cepetr/blue2joy/firmware/src/btjp/btjp_commands.c

/*
 * This file is part of the Blue2Joy project
 * (https://github.com/cepetr/blue2joy).
 * Copyright (c) 2025
 *
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
 * You should have received a copy of the GNU General Public License
 * along with this program. If not, see <http://www.gnu.org/licenses/>.
 */

#include <assert.h>
#include <stddef.h>
#include <string.h>
#include <stdlib.h>

#include <zephyr/logging/log.h>
#include <hw_id.h>
#include <app_version.h>

#include <devmgr/devmgr.h>
#include <mapper/mapper.h>
#include <mapper/joy_port.h>

#include "btjp.h"
#include "btjp_utils.h"
#include "btjp_msg.h"

LOG_MODULE_REGISTER(btj_cmd, LOG_LEVEL_DBG);

#define CHECK_REQ_SIZE(req, expected_size)                                                         \
    do {                                                                                           \
        if ((req)->hdr.size != (expected_size)) {                                                  \
            return BTJP_ERR_INVALID_REQ;                                                           \
        }                                                                                          \
    } while (0)

#define CHECK_REQ_ARG(condition)                                                                   \
    do {                                                                                           \
        if (!(condition)) {                                                                        \
            return BTJP_ERR_INVALID_ARG;                                                           \
        }                                                                                          \
    } while (0)

static void hw_id_get_bytes(uint8_t *buff, size_t buff_size)
{
    assert(buff_size == 8);

    memset(buff, 0, buff_size);

    // Get hexadecimal representation of HW ID
    char str[HW_ID_LEN];
    if (hw_id_get(str, sizeof(str)) != 0) {
        return;
    }

    // Parse hex string into bytes
    // (assumes valid hex string)
    for (size_t i = 0; i < buff_size; i++) {
        char byte_str[3] = {str[i * 2], str[i * 2 + 1], 0};
        buff[i] = (uint8_t)strtol(byte_str, NULL, 16);
    }
}

static btjp_status_t btjp_handle_request(const btjp_req_t *req, btjp_rsp_t *rsp)
{
    switch (req->hdr.msg_id) {
    case BTJP_MSG_GET_API_VERSION: {
        CHECK_REQ_SIZE(req, 0);
        rsp->hdr.size = sizeof(rsp->get_api_version);
        rsp->get_api_version.major = 1;
        rsp->get_api_version.minor = 0;
    } break;

    case BTJP_MSG_GET_SYS_INFO: {
        CHECK_REQ_SIZE(req, 0);
        rsp->hdr.size = sizeof(rsp->get_sys_info);
        hw_id_get_bytes(rsp->get_sys_info.hw_id, sizeof(rsp->get_sys_info.hw_id));
        rsp->get_sys_info.sw_version = APPVERSION;
        rsp->get_sys_info.hw_version = 0;
    } break;

    case BTJP_MSG_SET_DEV_CONFIG: {
        CHECK_REQ_SIZE(req, sizeof(req->set_dev_config));

        bt_addr_le_t addr;
        dev_addr_to_bt_addr_le(&req->set_dev_config.addr, &addr);

        devmgr_device_config_t config = {0};
        config.profile = req->set_dev_config.profile;

        int err = devmgr_set_device_config(&addr, &config, true);
        if (err != 0) {
            return BTJP_ERR_INVALID_ARG;
        }
    } break;

    case BTJP_MSG_SET_PIN_CONFIG: {
        CHECK_REQ_SIZE(req, sizeof(req->set_pin_config));

        mapper_profile_t profile;
        int err = mapper_get_profile(req->set_pin_config.profile, &profile);
        if (err != 0) {
            LOG_ERR("Invalid profile #%d", req->set_pin_config.profile);
            return BTJP_ERR_INVALID_ARG;
        }

        mapper_pin_config_t *config = profile_pin(&profile, req->set_pin_config.pin_id);
        if (config == NULL) {
            LOG_ERR("Invalid pin ID %d", req->set_pin_config.pin_id);
            return BTJP_ERR_INVALID_ARG;
        }

        config->source = req->set_pin_config.source;
        config->invert = req->set_pin_config.invert ? true : false;
        config->hat_switch = req->set_pin_config.hat_switch;
        config->threshold = req->set_pin_config.threshold;
        config->hysteresis = req->set_pin_config.hysteresis;

        err = mapper_set_profile(req->set_pin_config.profile, &profile, true);
        if (err != 0) {
            return BTJP_ERR_INVALID_ARG;
        }
    } break;

    case BTJP_MSG_SET_POT_CONFIG: {
        CHECK_REQ_SIZE(req, sizeof(req->set_pot_config));

        mapper_profile_t profile;
        int err = mapper_get_profile(req->set_pot_config.profile, &profile);
        if (err != 0) {
            LOG_ERR("Invalid profile #%d", req->set_pot_config.profile);
            return BTJP_ERR_INVALID_ARG;
        }

        mapper_pot_config_t *config = profile_pot(&profile, req->set_pot_config.pin_id);
        if (config == NULL) {
            LOG_ERR("Invalid pin ID %d", req->set_pot_config.pin_id);
            return BTJP_ERR_INVALID_ARG;
        }

        config->source = req->set_pot_config.source;
        config->low = req->set_pot_config.low;
        config->high = req->set_pot_config.high;

        err = mapper_set_profile(req->set_pot_config.profile, &profile, true);
        if (err != 0) {
            return BTJP_ERR_INVALID_ARG;
        }
    } break;

    case BTJP_MSG_SET_INTG_CONFIG: {
        CHECK_REQ_SIZE(req, sizeof(req->set_intg_config));

        mapper_profile_t profile;
        int err = mapper_get_profile(req->set_intg_config.profile, &profile);
        if (err != 0) {
            LOG_ERR("Invalid profile #%d", req->set_intg_config.profile);
            return BTJP_ERR_INVALID_ARG;
        }

        mapper_intg_config_t *config = profile_intg(&profile, req->set_intg_config.intg_id);
        if (config == NULL) {
            LOG_ERR("Invalid integrator ID %d", req->set_intg_config.intg_id);
            return BTJP_ERR_INVALID_ARG;
        }

        config->source = req->set_intg_config.source;
        config->mode = (mapper_intr_mode_t)req->set_intg_config.mode;
        config->dead_zone = req->set_intg_config.dead_zone;
        config->gain = req->set_intg_config.gain;
        config->max = req->set_intg_config.max;

        err = mapper_set_profile(req->set_intg_config.profile, &profile, true);
        if (err != 0) {
            return BTJP_ERR_INVALID_ARG;
        }
    } break;

    case BTJP_MSG_SET_MODE: {
        CHECK_REQ_SIZE(req, sizeof(req->set_mode));
        CHECK_REQ_ARG(req->set_mode.mode <= DEVMGR_MODE_MANUAL);

        devmgr_mode_t mode = (devmgr_mode_t)req->set_mode.mode;
        bool restart = req->set_mode.restart ? true : false;

        devmgr_set_mode(mode, restart);
    } break;

    case BTJP_MSG_SET_PROFILE: {
        CHECK_REQ_SIZE(req, sizeof(req->set_profile));

        mapper_profile_t profile = {0};

        for (int i = 0; i < ARRAY_SIZE(req->set_profile.pins); i++) {
            mapper_pin_config_t *pin = profile_pin(&profile, i);
            pin->source = req->set_profile.pins[i].source;
            pin->invert = req->set_profile.pins[i].invert ? true : false;
            pin->hat_switch = req->set_profile.pins[i].hat_switch;
            pin->threshold = req->set_profile.pins[i].threshold;
            pin->hysteresis = req->set_profile.pins[i].hysteresis;
        }

        for (int i = 0; i < ARRAY_SIZE(req->set_profile.pots); i++) {
            mapper_pot_config_t *pot = profile_pot(&profile, i);
            pot->source = req->set_profile.pots[i].source;
            pot->low = req->set_profile.pots[i].low;
            pot->high = req->set_profile.pots[i].high;
        }

        for (int i = 0; i < ARRAY_SIZE(req->set_profile.intgs); i++) {
            mapper_intg_config_t *intg = profile_intg(&profile, i);
            intg->source = req->set_profile.intgs[i].source;
            intg->mode = (mapper_intr_mode_t)req->set_profile.intgs[i].mode;
            intg->dead_zone = req->set_profile.intgs[i].dead_zone;
            intg->gain = req->set_profile.intgs[i].gain;
            intg->max = req->set_profile.intgs[i].max;
        }

        // Save updated profile
        int err = mapper_set_profile(req->set_profile.profile, &profile, true);
        if (err) {
            return BTJP_ERR_INVALID_ARG;
        }
    } break;

    case BTJP_MSG_FACTORY_RESET: {
        CHECK_REQ_SIZE(req, 0);
        LOG_ERR("Factory reset over BTJP is not implemented");
        return BTJP_ERR_UNKNOWN_MSG;
    } break;

    case BTJP_MSG_SET_JOY_PORT_MODE: {
        CHECK_REQ_SIZE(req, sizeof(req->set_joy_port_mode));

        joy_port_mode_t mode = JOY_PORT_MODE_NORMAL;

        switch (req->set_joy_port_mode.mode) {
        case BTJP_JOY_PORT_MODE_NORMAL:
            mode = JOY_PORT_MODE_NORMAL;
            break;
        case BTJP_JOY_PORT_MODE_SPI:
            mode = JOY_PORT_MODE_SPI;
            break;
        case BTJP_JOY_PORT_MODE_UART:
            mode = JOY_PORT_MODE_UART;
            break;
        default:
            return BTJP_ERR_INVALID_ARG;
        }

        int err = joy_port_set_mode(mode);
        if (err != 0) {
            return BTJP_ERR_INVALID_ARG;
        }
    } break;

    case BTJP_MSG_START_SCANNING: {
        CHECK_REQ_SIZE(req, 0);

        int err = devmgr_start_scanning();
        if (err != 0) {
            return BTJP_ERR_INVALID_ARG;
        }
    } break;

    case BTJP_MSG_STOP_SCANNING: {
        CHECK_REQ_SIZE(req, 0);

        devmgr_stop_scanning();
    } break;

    case BTJP_MSG_CONNECT_DEVICE: {
        CHECK_REQ_SIZE(req, sizeof(req->connect_device));

        bt_addr_le_t addr;
        dev_addr_to_bt_addr_le(&req->connect_device.addr, &addr);

        int err = devmgr_connect(&addr);
        if (err != 0) {
            return BTJP_ERR_INVALID_ARG;
        }
    } break;

    case BTJP_MSG_DELETE_DEVICE: {
        CHECK_REQ_SIZE(req, sizeof(req->delete_device));

        bt_addr_le_t addr;
        dev_addr_to_bt_addr_le(&req->delete_device.addr, &addr);

        int err = devmgr_delete_device(&addr);
        if (err != 0) {
            return BTJP_ERR_INVALID_ARG;
        }
    } break;

    case BTJP_MSG_PRESS_KEY: {
        CHECK_REQ_SIZE(req, sizeof(req->press_key));

        uint8_t keycode = req->press_key.keycode;

        mapper_press_key(keycode);
    } break;

    default:
        return BTJP_ERR_UNKNOWN_MSG;
    }

    return BTJP_ERR_NONE;
}

size_t btjp_handle_message(const void *inbuff, size_t insize, void *outbuff, size_t outsize)
{
    if (insize < sizeof(btjp_msg_header_t) || outsize < sizeof(btjp_rsp_t)) {
        LOG_ERR("Invalid buffer size");
        return 0;
    }

    const btjp_req_t *req = (const btjp_req_t *)inbuff;
    btjp_rsp_t *rsp = (btjp_rsp_t *)outbuff;

    if ((req->hdr.flags & BTJP_MSG_TYPE_MASK) != BTJP_MSG_TYPE_REQUEST) {
        // Not a request message
        LOG_ERR("Not a request message");
        return 0;
    }

    LOG_HEXDUMP_INF(inbuff, insize, "Received message");

    memset(rsp, 0, outsize);
    rsp->hdr.seq = req->hdr.seq;
    rsp->hdr.msg_id = req->hdr.msg_id;
    rsp->hdr.flags = BTJP_MSG_TYPE_RESPONSE;

    btjp_status_t status = btjp_handle_request(req, rsp);

    if (status != BTJP_ERR_NONE) {
        LOG_ERR("Request handling error {status: %d}", status);
        rsp->hdr.flags = BTJP_MSG_TYPE_ERROR;
        rsp->error.code = status;
        rsp->hdr.size = sizeof(rsp->error);
    }

    LOG_HEXDUMP_INF(outbuff, sizeof(btjp_msg_header_t) + rsp->hdr.size, "Sending response");

    return sizeof(btjp_msg_header_t) + rsp->hdr.size;
}

// Checks whether the buffer contains a BTJP_MSG_GET_API_VERSION request.
bool btjp_is_sync_request(const uint8_t *inbuff, size_t insize)
{
    if (insize < sizeof(btjp_msg_header_t)) {
        return false;
    }

    const btjp_msg_header_t *hdr = (const btjp_msg_header_t *)inbuff;

    return (hdr->flags & BTJP_MSG_TYPE_MASK) == BTJP_MSG_TYPE_REQUEST &&
           hdr->msg_id == BTJP_MSG_GET_API_VERSION;
}
