cepetr/blue2joy/firmware/src/io/io_pot.c

/*
 * This file is part of the Blue2Joy project
 * (https://github.com/cepetr/blue2joy).
 * Copyright (c) 2025
 *
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
 * You should have received a copy of the GNU General Public License
 * along with this program. If not, see <http://www.gnu.org/licenses/>.
 */

#include <zephyr/kernel.h>
#include <zephyr/logging/log.h>
#include <zephyr/drivers/gpio.h>
#include <zephyr/irq.h>

#include <nrfx_comp.h>
#include <nrfx_timer.h>
#include <nrfx_ppi.h>
#include <nrfx_gpiote.h>

#include "io_pot.h"

LOG_MODULE_REGISTER(btj_io_pot, LOG_LEVEL_DBG);

static const nrfx_timer_t timer = NRFX_TIMER_INSTANCE(2);
static const nrfx_gpiote_t gpiote = NRFX_GPIOTE_INSTANCE(0);

static const struct gpio_dt_spec joy_p0_chg = GPIO_DT_SPEC_GET(DT_ALIAS(joy_p0_chg), gpios);

typedef struct {
    uint8_t keycodes[8];
    uint8_t count;
    bool pressed;
} io_pot_kbd_t;

typedef struct {
    uint8_t gpiote_p0_chg; // GPIOTE channel for POT0 charging
    uint8_t gpiote_p1_chg; // GPIOTE channel for POT1 charging

    nrf_ppi_channel_t ppi_start_cycle; // PPI channel to start the timer cycle
    nrf_ppi_channel_t ppi_p0_charge;   // PPI channel for POT0 charging
    nrf_ppi_channel_t ppi_p1_charge;   // PPI channel for POT1 charging
    nrf_ppi_channel_t ppi_end_cycle;   // PPI channel to end the timer cycle

    // Simple averaging filter state
    struct {
        uint8_t buf[10];
        uint8_t pos;
        uint16_t sum;
        uint32_t time;
    } filter;

    // Measured period in milliseconds
    atomic_t period;

    atomic_t cc_value[IO_POT_COUNT];

    // Encoder simulator position
    int32_t enc_pos[IO_POT_COUNT];

    // Keyboard simulation
    io_pot_kbd_t kbd;

} io_pot_drv_t;

io_pot_drv_t g_io_pot_drv;

// Forward declarations
static void io_pot_process_keypresses(void);

static void comparator_handler(nrf_comp_event_t event)
{
    io_pot_drv_t *drv = &g_io_pot_drv;

    uint32_t now = k_uptime_get_32();

    if (drv->filter.time > 0) {
        uint32_t diff = now - drv->filter.time;

        // Calculate moving average
        drv->filter.sum -= drv->filter.buf[drv->filter.pos];
        drv->filter.buf[drv->filter.pos] = diff;
        drv->filter.sum += drv->filter.buf[drv->filter.pos];
        drv->filter.pos = (drv->filter.pos + 1) % ARRAY_SIZE(drv->filter.buf);
    }

    atomic_set(&drv->period, (drv->filter.sum / ARRAY_SIZE(drv->filter.buf)));

    drv->filter.time = now;

    // Process pending key presses for keyboard emulation
    io_pot_process_keypresses();
}

static void timer_handler(nrf_timer_event_t event_type, void *p_context)
{
    io_pot_drv_t *drv = &g_io_pot_drv;

    // Since TIMER CC registers are not double buffered, we need to
    // update them in the timer interrupt handler - just after the
    // compare event has occurred.

    if (event_type == NRF_TIMER_EVENT_COMPARE0) {
        uint32_t cc_value = atomic_get(&drv->cc_value[0]);
        nrfx_timer_compare(&timer, NRF_TIMER_CC_CHANNEL0, cc_value, true);
    } else if (event_type == NRF_TIMER_EVENT_COMPARE1) {
        uint32_t cc_value = atomic_get(&drv->cc_value[1]);
        nrfx_timer_compare(&timer, NRF_TIMER_CC_CHANNEL1, cc_value, true);
    }
}

int io_pot_init(void)
{
    io_pot_drv_t *drv = &g_io_pot_drv;

    nrfx_gpiote_pin_t pin_p0_chg = NRF_GPIO_PIN_MAP(0, 15); // Pin for POT0 charging
    nrfx_gpiote_pin_t pin_p1_chg = NRF_GPIO_PIN_MAP(0, 19); // Pin for POT1 charging

    // Get pin/port from joy_p0_chg
    gpio_pin_configure_dt(&joy_p0_chg, GPIO_OUTPUT_LOW);

    // -------------------------------------------------------------------------------
    // Initialize the analog comparator
    //
    // V+ = (Vcap + 5V) / 4 - when POT0 charging is active
    // V+ = Vcap / 2 - when POT0 charging is inactive
    // V- = 1.4V (Upper threshold) or 1.3V (Lower threshold)
    //
    // The comparator is used to monitor the POT0 voltage in order to detect
    // when the POKEY chip releases its discharge transistors,
    // indicating that the POKEY counter has been reset and starts counting.
    //
    // The comparator is automatically stopped after the UP event
    // and is started again at the end of the cycle (which is set to 17 ms).
    // -------------------------------------------------------------------------------

    nrfx_comp_config_t comp_config = NRFX_COMP_DEFAULT_CONFIG(NRF_COMP_INPUT_4);

    comp_config.reference = NRF_COMP_REF_INT_2V4;
    comp_config.main_mode = NRF_COMP_MAIN_MODE_SE;
    comp_config.threshold.th_down = NRFX_COMP_VOLTAGE_THRESHOLD_TO_INT(1.3, 2.4);
    comp_config.threshold.th_up = NRFX_COMP_VOLTAGE_THRESHOLD_TO_INT(1.4, 2.4);
    comp_config.speed_mode = NRF_COMP_SP_MODE_HIGH;
    comp_config.hyst = NRF_COMP_HYST_NO_HYST;

    nrfx_err_t err;

    err = nrfx_comp_init(&comp_config, comparator_handler);
    if (err != NRFX_SUCCESS) {
        LOG_ERR("nrfx_comp_init error: %08x", err);
        return -EIO;
    }

    // Connect COMP_IRQ to nrfx_comp_irq_handler - TODO: do we need this??
    IRQ_CONNECT(COMP_LPCOMP_IRQn, IRQ_PRIO_LOWEST, nrfx_isr, nrfx_comp_irq_handler, 0);

    nrfx_comp_start(NRF_COMP_INT_UP_MASK, NRFX_COMP_SHORT_STOP_AFTER_UP_EVT);

    // -------------------------------------------------------------------------------
    // Initialize the timer
    //
    // The timer is used to precisely control the charging outputs
    // of the POT0 and POT1 capacitors. It is started a few microseconds after
    // we detect that the POKEY chip has released its discharge transistors.
    //
    // Two compare channels are used to control the time when we
    // activate the MOSFETs that rapidly charge the POT0 and POT1 capacitors.
    //
    // Channel 0 - triggers POT0 charging
    // Channel 1 - triggers POT1 charging
    // Channel 2 - starts comparator
    // Channel 3 - resets the timer
    // -------------------------------------------------------------------------------

    nrfx_timer_config_t timer_config = NRFX_TIMER_DEFAULT_CONFIG(NRFX_MHZ_TO_HZ(1));
    timer_config.mode = NRF_TIMER_MODE_TIMER;
    timer_config.bit_width = NRF_TIMER_BIT_WIDTH_16;

    err = nrfx_timer_init(&timer, &timer_config, timer_handler);
    if (err != NRFX_SUCCESS) {
        LOG_ERR("nrfx_timer_init error: %08x", err);
        return -EIO;
    }

    IRQ_CONNECT(TIMER2_IRQn, IRQ_PRIO_LOWEST, nrfx_isr, nrfx_timer_2_irq_handler, 0)

    uint32_t initial_cc_value = 16000; // => IO_POT_MAX_VAL

    atomic_set(&drv->cc_value[0], initial_cc_value);
    atomic_set(&drv->cc_value[1], initial_cc_value);

    nrfx_timer_compare(&timer, NRF_TIMER_CC_CHANNEL0, initial_cc_value, true);
    nrfx_timer_compare(&timer, NRF_TIMER_CC_CHANNEL1, initial_cc_value, true);

    nrfx_timer_compare(&timer, NRF_TIMER_CC_CHANNEL2, 17000, false); // 17ms

    nrfx_timer_extended_compare(&timer, NRF_TIMER_CC_CHANNEL3, 25000,
                                NRF_TIMER_SHORT_COMPARE3_CLEAR_MASK, false);

    nrfx_timer_enable(&timer);

    // -------------------------------------------------------------------------------
    // Outputs for capacitor charging
    //
    // The POT0 and POT1 charging outputs are controlled by GPIOTE,
    // allowing us to activate them via PPI channels.
    // -------------------------------------------------------------------------------

    // POT0 charging

    err = nrfx_gpiote_channel_alloc(&gpiote, &drv->gpiote_p0_chg);
    if (err != NRFX_SUCCESS) {
        LOG_ERR("nrfx_gpiote_channel_alloc error: %08x", err);
        return -EIO;
    }

    nrfx_gpiote_output_config_t out_config = NRFX_GPIOTE_DEFAULT_OUTPUT_CONFIG;

    nrfx_gpiote_task_config_t task_config = {
        .task_ch = drv->gpiote_p0_chg,
        .polarity = GPIOTE_CONFIG_POLARITY_LoToHi,
        .init_val = NRF_GPIOTE_INITIAL_VALUE_LOW,
    };

    err = nrfx_gpiote_output_configure(&gpiote, pin_p0_chg, &out_config, &task_config);
    if (err != NRFX_SUCCESS) {
        LOG_ERR("nrfx_gpiote_out_init error: %08x", err);
        return -EIO;
    }

    nrfx_gpiote_out_task_enable(&gpiote, pin_p0_chg);

    // POT1 charging

    err = nrfx_gpiote_channel_alloc(&gpiote, &drv->gpiote_p1_chg);
    if (err != NRFX_SUCCESS) {
        LOG_ERR("nrfx_gpiote_channel_alloc error: %08x", err);
        return -EIO;
    }

    nrfx_gpiote_output_config_t out_config2 = NRFX_GPIOTE_DEFAULT_OUTPUT_CONFIG;

    nrfx_gpiote_task_config_t task_config2 = {
        .task_ch = drv->gpiote_p1_chg,
        .polarity = GPIOTE_CONFIG_POLARITY_LoToHi,
        .init_val = NRF_GPIOTE_INITIAL_VALUE_LOW,
    };

    err = nrfx_gpiote_output_configure(&gpiote, pin_p1_chg, &out_config2, &task_config2);
    if (err != NRFX_SUCCESS) {
        LOG_ERR("nrfx_gpiote_out_init error: %08x", err);
        return -EIO;
    }

    nrfx_gpiote_out_task_enable(&gpiote, pin_p1_chg);

    // -------------------------------------------------------------------------------
    // PPI channels
    //
    // PPI channels connect the analog comparator, timer, and GPIOTE peripherals.
    //
    // PPI usage:
    // 1. COMP_UP event -> TIMER_CLEAR task & GPIOTE_CLR task (disable POT0 charging)
    // 2. TIMER_COMPARE0 event -> GPIOTE_SET task (enable POT0 charging)
    // 3. TIMER_COMPARE1 event -> GPIOTE_SET task (enable POT1 charging)
    // 4. TIMER_COMPARE3 event -> COMP_START task (restart comparator)
    // -------------------------------------------------------------------------------

    uint32_t eep;
    uint32_t tep;

    // --------------------------------------------------------------------
    // ppi_start_cycle
    //
    // Comparator UP event:
    //   -> clears the timer
    //   -> disables the POT0 charging output

    err = nrfx_ppi_channel_alloc(&drv->ppi_start_cycle);
    if (err != NRFX_SUCCESS) {
        LOG_ERR("nrfx_ppi_channel_alloc error: %08x", err);
        return -EIO;
    }

    eep = nrfx_comp_event_address_get(NRF_COMP_EVENT_UP);
    tep = nrfx_timer_task_address_get(&timer, NRF_TIMER_TASK_CLEAR);

    err = nrfx_ppi_channel_assign(drv->ppi_start_cycle, eep, tep);
    if (err != NRFX_SUCCESS) {
        LOG_ERR("nrfx_ppi_channel_assign error: %08x", err);
        return -EIO;
    }

    tep = nrfx_gpiote_clr_task_address_get(&gpiote, pin_p0_chg);
    err = nrfx_ppi_channel_fork_assign(drv->ppi_start_cycle, tep);
    if (err != NRFX_SUCCESS) {
        LOG_ERR("nrfx_ppi_channel_fork_assign error: %08x", err);
        return -EIO;
    }

    err = nrfx_ppi_channel_enable(drv->ppi_start_cycle);
    if (err != NRFX_SUCCESS) {
        LOG_ERR("Failed enabling ppi channel: %08x", err);
        return -EIO;
    }

    // --------------------------------------------------------------------
    // ppi_p0_charge
    //
    // Timer COMPARE0 event:
    //   -> enables the POT0 charging output

    err = nrfx_ppi_channel_alloc(&drv->ppi_p0_charge);
    if (err != NRFX_SUCCESS) {
        LOG_ERR("nrfx_ppi_channel_alloc error: %08x", err);
        return -EIO;
    }

    eep = nrfx_timer_event_address_get(&timer, NRF_TIMER_EVENT_COMPARE0);
    tep = nrfx_gpiote_set_task_address_get(&gpiote, pin_p0_chg);

    err = nrfx_ppi_channel_assign(drv->ppi_p0_charge, eep, tep);
    if (err != NRFX_SUCCESS) {
        LOG_ERR("nrfx_ppi_channel_assign error: %08x", err);
        return -EIO;
    }

    err = nrfx_ppi_channel_enable(drv->ppi_p0_charge);
    if (err != NRFX_SUCCESS) {
        LOG_ERR("Failed enabling ppi channel: %08x", err);
        return -EIO;
    }

    // --------------------------------------------------------------------
    // ppi_p1_charge
    //
    // Timer COMPARE1 event:
    //   -> enables the POT1 charging output

    err = nrfx_ppi_channel_alloc(&drv->ppi_p1_charge);
    if (err != NRFX_SUCCESS) {
        LOG_ERR("nrfx_ppi_channel_alloc error: %08x", err);
        return -EIO;
    }

    eep = nrfx_timer_event_address_get(&timer, NRF_TIMER_EVENT_COMPARE1);
    tep = nrfx_gpiote_set_task_address_get(&gpiote, pin_p1_chg);

    err = nrfx_ppi_channel_assign(drv->ppi_p1_charge, eep, tep);
    if (err != NRFX_SUCCESS) {
        LOG_ERR("nrfx_ppi_channel_assign error: %08x", err);
        return -EIO;
    }

    err = nrfx_ppi_channel_enable(drv->ppi_p1_charge);
    if (err != NRFX_SUCCESS) {
        LOG_ERR("Failed enabling ppi channel: %08x", err);
        return -EIO;
    }

    // --------------------------------------------------------------------
    // ppi_end_cycle
    //
    // Timer COMPARE2 event:
    //   -> restarts the comparator (which was automatically stopped on UP event)
    //   -> disables the POT1 charging output

    err = nrfx_ppi_channel_alloc(&drv->ppi_end_cycle);
    if (err != NRFX_SUCCESS) {
        LOG_ERR("nrfx_ppi_channel_alloc error: %08x", err);
        return -EIO;
    }

    eep = nrfx_timer_event_address_get(&timer, NRF_TIMER_EVENT_COMPARE2);
    tep = nrfx_comp_task_address_get(NRF_COMP_TASK_START);

    err = nrfx_ppi_channel_assign(drv->ppi_end_cycle, eep, tep);
    if (err != NRFX_SUCCESS) {
        LOG_ERR("nrfx_ppi_channel_assign error: %08x", err);
        return -EIO;
    }

    tep = nrfx_gpiote_clr_task_address_get(&gpiote, pin_p1_chg);
    err = nrfx_ppi_channel_fork_assign(drv->ppi_end_cycle, tep);
    if (err != NRFX_SUCCESS) {
        LOG_ERR("nrfx_ppi_channel_fork_assign error: %08x", err);
        return -EIO;
    }

    err = nrfx_ppi_channel_enable(drv->ppi_end_cycle);
    if (err != NRFX_SUCCESS) {
        LOG_ERR("Failed enabling ppi channel: %08x", err);
        return -EIO;
    }

    LOG_INF("io_pot initialized");
    return 0;
}

void io_pot_set(uint8_t pot_idx, int value)
{
    io_pot_drv_t *drv = &g_io_pot_drv;

    if (pot_idx >= ARRAY_SIZE(drv->cc_value)) {
        return;
    }

    LOG_INF("io_pot_set: pot_idx=%d, value=%d", pot_idx, value);

    value = CLAMP(value, IO_POT_MIN_VAL, IO_POT_MAX_VAL);

    if (value == IO_POT_MAX_VAL) {
        // Ensure the CC value is long enough so Pokey reads 228 safely
        value = IO_POT_MAX_VAL + 5;
    }

    // Ideally, we should calculate cc_value as 64 * (value - IO_POT_MIN_VAL),
    // but due to inaccuracies between the Atari and nRF crystals, I adjusted the
    // formula experimentally to get more accurate results (works well on my HW).
    uint32_t us = (642 * (value - IO_POT_MIN_VAL)) / 10 + 32;

    atomic_set(&drv->cc_value[pot_idx], us);
}

int io_pot_get(uint8_t pot_idx)
{
    io_pot_drv_t *drv = &g_io_pot_drv;

    if (pot_idx >= ARRAY_SIZE(drv->cc_value)) {
        return IO_POT_MAX_VAL;
    }

    uint32_t us = atomic_get(&drv->cc_value[pot_idx]);

    // Reverse of the formula in io_pot_set()
    int value = ((us - 32) * 10) / 642 + IO_POT_MIN_VAL;

    return CLAMP(value, IO_POT_MIN_VAL, IO_POT_MAX_VAL);
}

void io_pot_update_encoder(uint8_t pot_idx, int32_t delta, int32_t max)
{
    io_pot_drv_t *drv = &g_io_pot_drv;

    if (pot_idx >= ARRAY_SIZE(drv->enc_pos)) {
        return;
    }

    unsigned int key = irq_lock();
    drv->enc_pos[pot_idx] = CLAMP(drv->enc_pos[pot_idx] + delta, -max << 14, max << 14);
    irq_unlock(key);
}

void io_pot_send_keypress(uint8_t keycode)
{
    io_pot_drv_t *drv = &g_io_pot_drv;

    io_pot_kbd_t *kbd = &drv->kbd;

    if (kbd->count >= ARRAY_SIZE(kbd->keycodes)) {
        return;
    }

    unsigned int key = irq_lock();
    kbd->keycodes[kbd->count] = keycode;
    ++kbd->count;
    irq_unlock(key);
}

// This function must be called with disabled interrupts
static void io_pot_process_keypresses(void)
{
    io_pot_drv_t *drv = &g_io_pot_drv;

    io_pot_kbd_t *kbd = &drv->kbd;

    if (kbd->count == 0 && !kbd->pressed) {
        return;
    }

    if (!kbd->pressed) {
        // Send keycode
        uint8_t lo = 4 + ((kbd->keycodes[0] & 0x0F) << 3);
        uint8_t hi = 4 + ((kbd->keycodes[0] >> 4) << 3);
        io_pot_set(0, lo);
        io_pot_set(1, hi);
        kbd->pressed = true;
    } else {
        // Send release
        io_pot_set(0, IO_POT_MAX_VAL);
        io_pot_set(1, IO_POT_MAX_VAL);

        // Shift keycodes
        for (uint8_t i = 1; i < kbd->count; i++) {
            kbd->keycodes[i - 1] = kbd->keycodes[i];
        }
        kbd->count--;
        kbd->pressed = false;
    }
}
