cepetr/blue2joy/firmware/src/xep80/xep80_cmd.c

/*
 * This file is part of the Blue2Joy project
 * (https://github.com/cepetr/blue2joy).
 * Copyright (c) 2025
 *
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
 * You should have received a copy of the GNU General Public License
 * along with this program. If not, see <http://www.gnu.org/licenses/>.
 */

#include <io/xep80_uart.h>

#include "xep80_internal.h"

// Moves cursor vertically up to the start of the current logical line
// (horizonal position is not changed)
static void move_to_logical_start(xep80_t *xep)
{
    while (xep->cur.y > 0 && !xep80_last_row_in_line(xep, xep->cur.y - 1)) {
        xep->cur.y--;
    }
}

// Reads character at current cursor position and
// advances cursor to the next position,
static void read_char_and_advance(xep80_t *xep)
{
    xep80_uart_send(xep80_vram_get(xep, xep->cur.x, xep->cur.y));

    if (xep->cur.x < xep->r_margin) {
        xep->cur.x++;
    } else {
        xep->cur.x = xep->l_margin;
        if (xep->cur.y < XEP80_STATUS_LINE) {
            xep->cur.y++;
        } else {
            xep->cur.y = 0;
        }
    }

    xep80_sync_cursor(xep);
}

static void set_character_set(xep80_t *xep, uint8_t charset)
{
    if (charset > 2) {
        return;
    }

    xep->state.srow = xep->state.rows[XEP80_STATUS_LINE] * XEP80_ROW_SIZE;

    if (charset < 2) {
        xep->state.vcr |= 0x80; // External charset
    } else {
        xep->state.vcr &= ~0x80; // Internal charset
    }

    for (int i = 0; i < XEP80_ROW_COUNT; i++) {
        xep->state.rows[i] = (xep->state.rows[i] & 0x9F) | (charset << 5);
    }
}

void xep80_process_cmd(xep80_t *xep, uint16_t cmd)
{
    switch (cmd) {
    case 0x199: // Set graphics
        break;

    case 0x19A: // Modify graphics to 50Hz
        break;

    case 0x1C0:
        read_char_and_advance(xep);
        break;

    case 0x1C1:
        // Read horizontal position
        xep80_uart_send(xep->cur.x);
        break;

    case 0x1C2:
        // Master reset
        xep80_reset(xep);
        xep80_uart_send(0x01);
        break;

    case 0x1C3:
        // Get printer status
        xep80_uart_send(0x01);
        break;

    case 0x1C4:
        // Fill VRAM with the most recently received character
        memset(xep->state.vram, xep->last_char, sizeof(xep->state.vram));
        xep80_uart_send(0x01);
        break;

    case 0x1C5:
        // Fill VRAM with spaces
        memset(xep->state.vram, 0x20, sizeof(xep->state.vram));
        xep80_uart_send(0x01);
        break;

    case 0x1C6:
        // Fill VRAM with EOL (0x9B)
        memset(xep->state.vram, 0x9B, sizeof(xep->state.vram));
        xep80_uart_send(0x01);
        break;

    case 0x1C7:
        // Read char at cursor position without advancing cursor
        xep80_uart_send(xep80_vram_get(xep, xep->cur.x, xep->cur.y));
        break;

    case 0x1D0:
        // Clear list flag
        xep->escape_mode = false;
        break;

    case 0x1D1:
        xep->escape_mode = true;
        break;

    case 0x1D2:
        // Disable burst mode
        xep->burst_mode = false;
        xep->printer_mode = false;
        break;

    case 0x1D3:
        // Enable burst mode
        xep->burst_mode = true;
        xep->printer_mode = false;
        break;

    case 0x1D4:
        // Set ATASCII character set
        set_character_set(xep, 0);
        break;

    case 0x1D5:
        // Set international character set
        set_character_set(xep, 1);
        break;

    case 0x1D6:
        // Set internal character set
        set_character_set(xep, 2);
        break;

    case 0x1D7:
        // Modify text display to 50Hz
        // TODO
        break;

    case 0x1D8:
        // Cursor off
        xep->state.vcr |= 0x02; // Static cursor
        xep->cursor_on = false;
        break;

    case 0x1D9:
        // Cursor on
        xep->state.vcr |= 0x02; // Static cursor
        xep->cursor_on = true;
        break;

    case 0x1DA:
        // Cursor blink on
        xep->state.vcr &= ~0x02; // Blinking cursor
        xep->cursor_on = true;
        break;

    case 0x1DB:
        move_to_logical_start(xep);
        break;

    case 0x1DC:
        // Set scroll window to current cursor x position
        xep->state.x_scroll = xep->cur.x;
        break;

    case 0x1DD:
        // Redirect character output to printer
        xep->printer_mode = true;
        xep->burst_mode = true;
        break;

    case 0x1DE:
        // White on black
        xep->state.vcr &= ~0x08; // Reverse video flag
        break;

    case 0x1DF:
        // Black on white
        xep->state.vcr |= 0x08; // Reverse video flag
        break;

    case 0x1E1:
    case 0x1E4:
    case 0x1E6:
    case 0x1EE:
    case 0x1F0:
    case 0x1F2:
    case 0x1F9:
        // Set extra byte
        xep->extra_byte = xep->last_char;
        break;

    case 0x1ED:
        // Set VCR register
        xep->state.vcr = xep->last_char;
        break;

    case 0x1F4:
        // Set attribute latch 0
        xep->state.attr0 = xep->last_char;
        break;

    case 0x1F5:
        // Set attribute latch 1
        xep->state.attr1 = xep->last_char;
        break;

    case 0x1F6:
        // Set TCP register
        xep->tcp_register = xep->last_char & 0xF;
        break;

    case 0x1F7:
        // Write TCP register
        xep->state.tcp[xep->tcp_register] = xep->last_char;
        xep->tcp_register = (xep->tcp_register + 1) & 0xF;
        break;

    case 0x1FA:
        // Set PSR register
        // TODO
        break;

    case 0x1FB:
        // Set UCR regisgter
        // TODO
        break;

    case 0x1FC:
        // Set UMX register
        // TODO
        break;

    case 0x1FD:
        // Retransmit last character
        xep80_uart_send(xep->last_char);
        break;

    default:
        if (cmd >= 0x100 && cmd <= 0x14F) {
            // Set horizontal position (0-79)
            xep->cur.x = cmd & 0xFF;
            xep->synced_cur = xep->cur;
        } else if (cmd >= 0x150 && cmd <= 0x15F) {
            // Set horizontal cur position
            xep->cur.x = (xep->cur.x & 0x0F) | ((cmd & 0xF) << 4);
            xep->synced_cur = xep->cur;
        } else if (cmd >= 0x160 && cmd <= 0x16F) {
            // Set left margin (low nibble)
            xep->l_margin = cmd & 0xF;
        } else if (cmd >= 0x170 && cmd <= 0x17F) {
            // Set left margin (high nibble)
            xep->l_margin = (xep->l_margin & 0x0F) | ((cmd & 0xF) << 4);
        } else if (cmd >= 0x180 && cmd <= 0x197) {
            // Set vertical position (0-23)
            xep->cur.y = cmd & 0x1F;
            xep->synced_cur = xep->cur;
        } else if (cmd == 0x198) {
            // Set status line

            // The XEP80.SYS driver occasionally sends an unexpected 0x198 command
            // that completely messes up the screen, so ignore it for now.
            // TODO: investigate and fix the root cause.

            // xep->cur.y = XEP80_STATUS_LINE;
            // xep->synced_cur = xep->cur;
        } else if (cmd >= 0x1A0 && cmd <= 0x1AF) {
            // Set right margin (low nibble)
            xep->r_margin = 0x40 + (cmd & 0xF);
        } else if (cmd >= 0x1B0 && cmd <= 0x1BF) {
            // Set right margin (high nibble)
            xep->r_margin = (xep->r_margin & 0x0F) | ((cmd & 0xF) << 4);
        }
    }
}
